mbouhier/HASOR_files/3D printing/stl files/bloceur_alim.stl

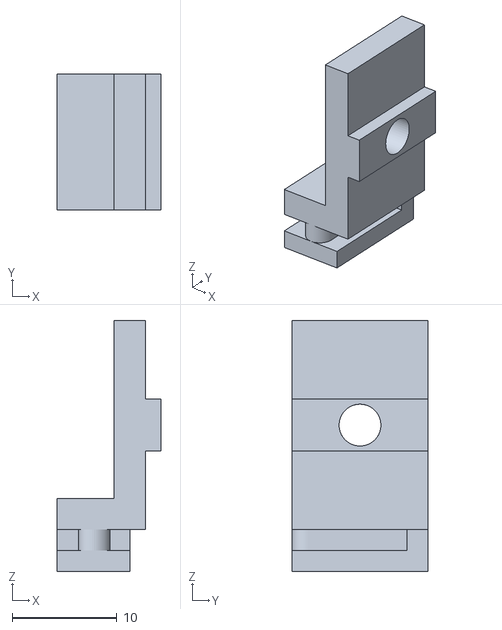
[picture p16: CAD file, 2023-03-02]
3D printing/stl files/bloceur_alim.stl
9.96 x 13.0 x 24.0
