mbouhier/HASOR_files/3D printing/stl files/end_stop_40mm_v3.stl

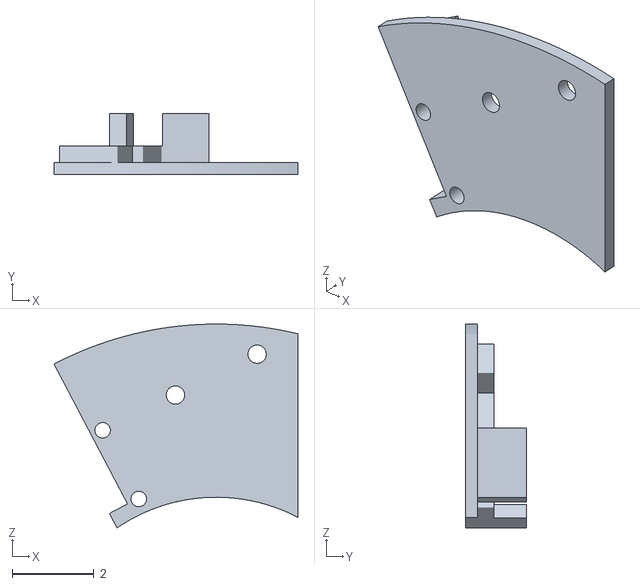
[picture p17: CAD file, 2023-03-02]
3D printing/stl files/end_stop_40mm_v3.stl
5.97 x 1.50 x 4.99
