mbouhier/HASOR_files/3D printing/stl files/support_fourche_principal_simplifie4.stl

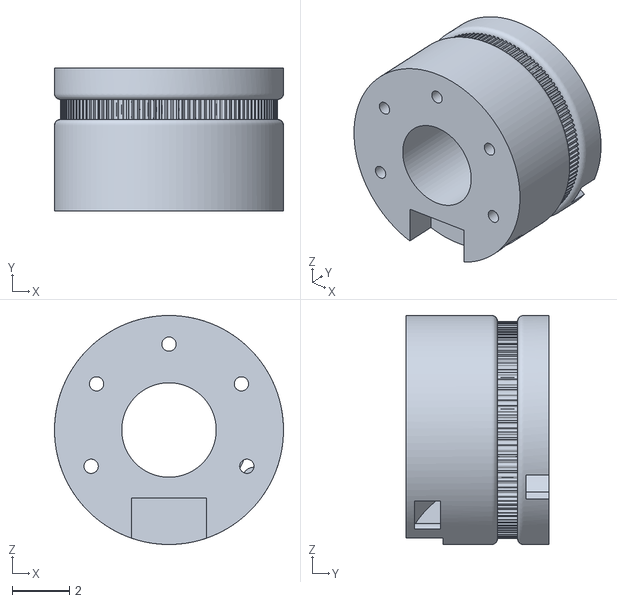
[picture p18: CAD file, 2023-03-02]
3D printing/stl files/support_fourche_principal_simplifie4.stl
8.00 x 5.00 x 8.00
