mbouhier/HASOR_files/3D printing/stl files/espaceur_20mm_v4.stl

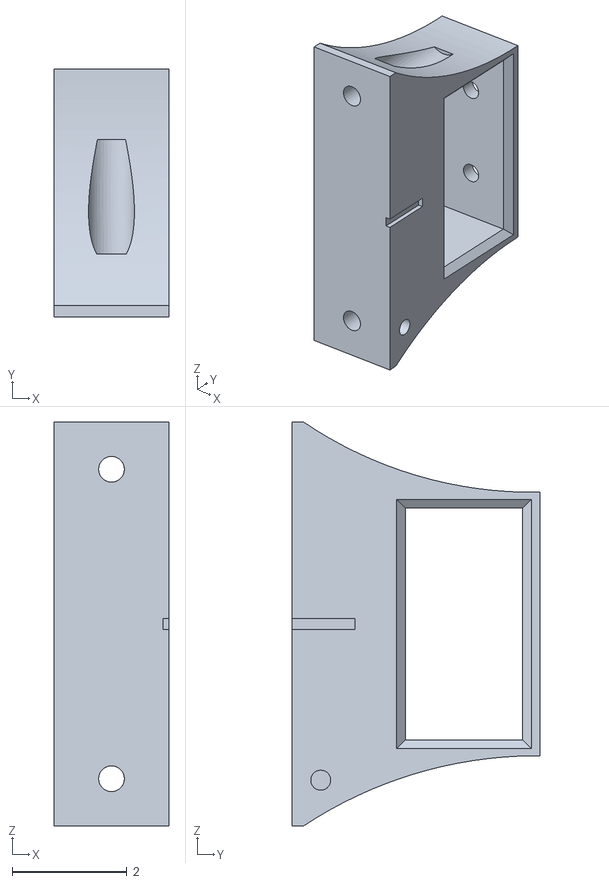
[picture p19: CAD file, 2023-03-02]
3D printing/stl files/espaceur_20mm_v4.stl
2.00 x 4.32 x 7.05
