mbouhier/HASOR_files/3D printing/stl files/support_plateau_v3.stl

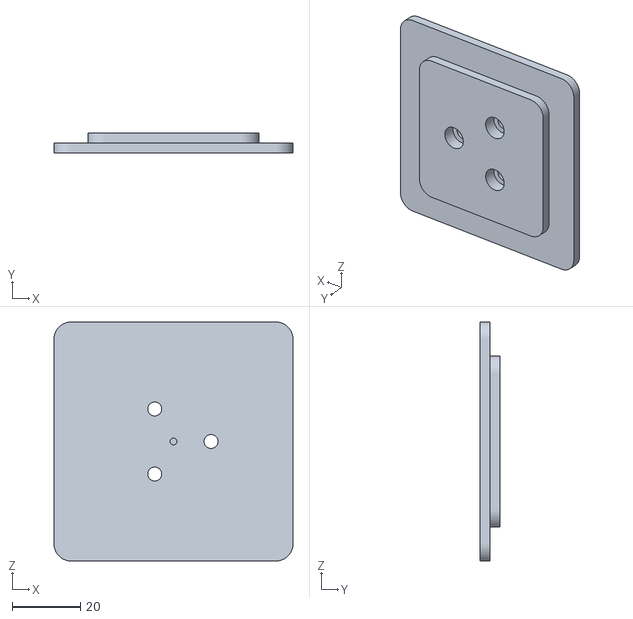
[picture p20: CAD file, 2023-03-02]
3D printing/stl files/support_plateau_v3.stl
70.0 x 6.00 x 70.0
