mbouhier/HASOR_files/3D printing/stl files/support_nema17_40mm.stl

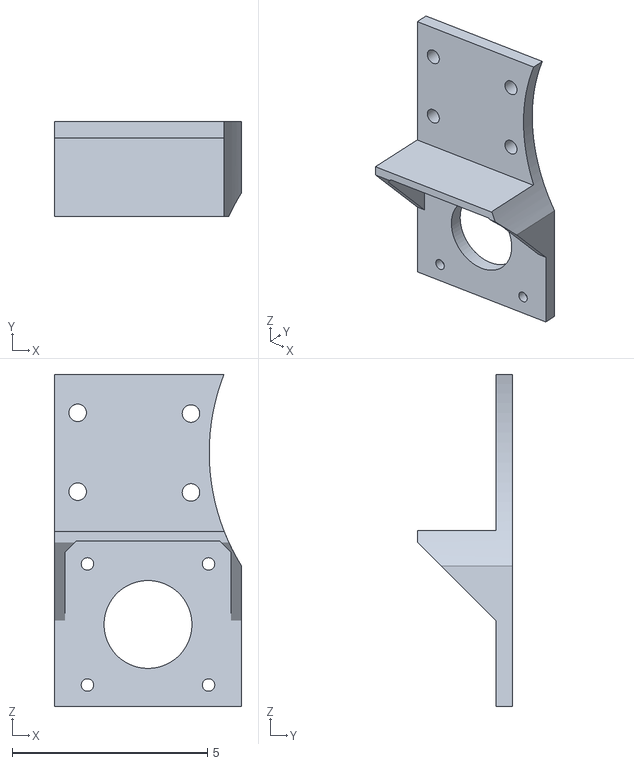
[picture p21: CAD file, 2023-03-02]
3D printing/stl files/support_nema17_40mm.stl
4.80 x 2.42 x 8.50
