mbouhier/HASOR_files/3D printing/stl files/bas_de_fourche_gros_bloc.stl

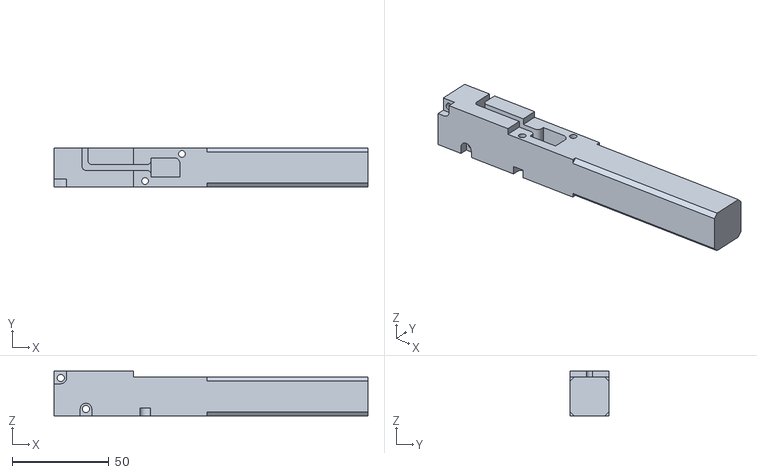
[picture p22: CAD file, 2023-03-02]
3D printing/stl files/bas_de_fourche_gros_bloc.stl
162.0 x 20.0 x 23.0
