mbouhier/HASOR_files/3D printing/stl files/support_fourche_partie_clef.stl

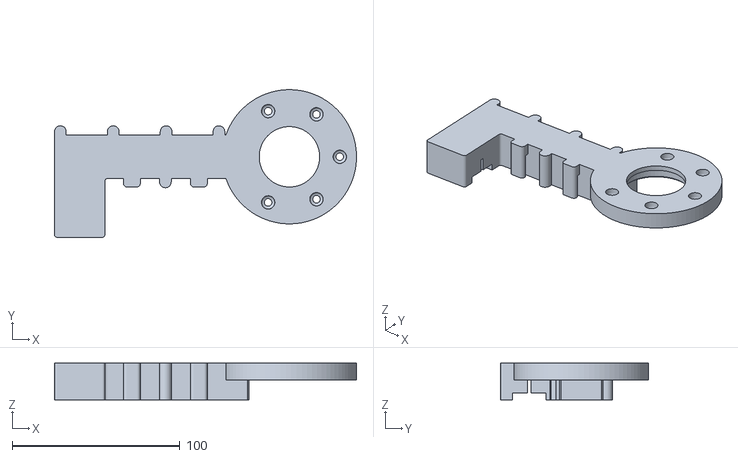
[picture p23: CAD file, 2023-03-02]
3D printing/stl files/support_fourche_partie_clef.stl
180.0 x 88.0 x 22.0
