mbouhier/HASOR_files/3D printing/stl files/guide_nappe_led.stl

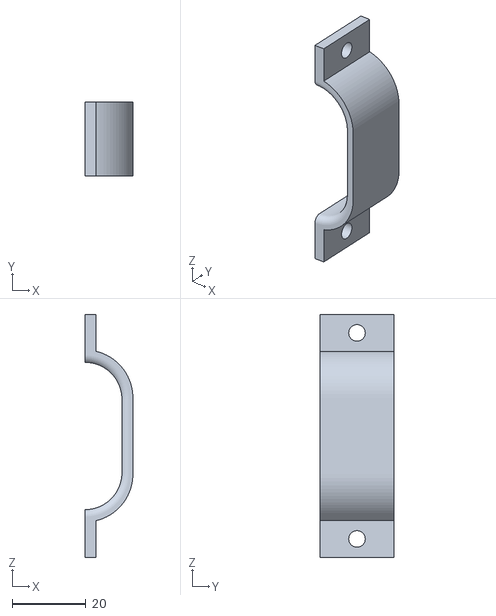
[picture p24: CAD file, 2023-03-02]
3D printing/stl files/guide_nappe_led.stl
13.0 x 20.0 x 66.0
