mbouhier/HASOR_files/3D printing/stl files/fourche_v2_sans_radiateurs.stl

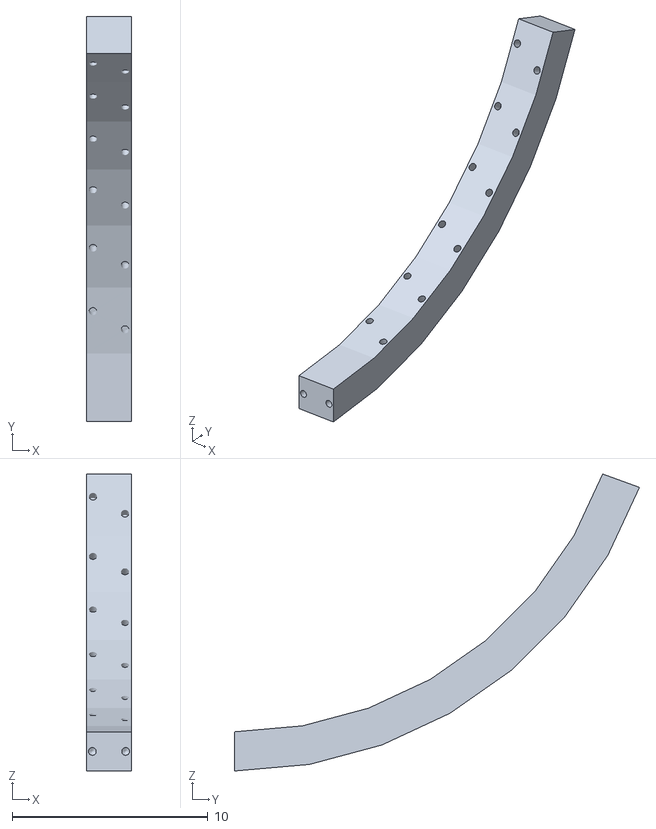
[picture p25: CAD file, 2023-03-02]
3D printing/stl files/fourche_v2_sans_radiateurs.stl
2.30 x 20.7 x 15.2
