mbouhier/HASOR_files/3D printing/stl files/support arduino_v2.stl

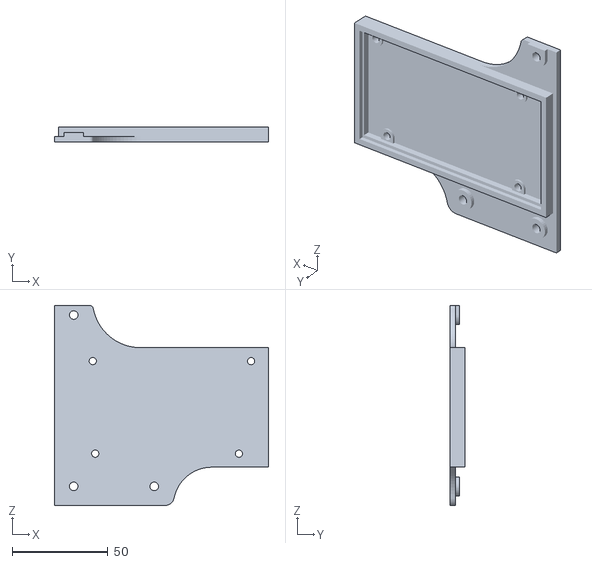
[picture p26: CAD file, 2023-03-02]
3D printing/stl files/support arduino_v2.stl
111.6 x 8.00 x 104.3
