mbouhier/HASOR_files/3D printing/stl files/end_stop_plug_v3.stl

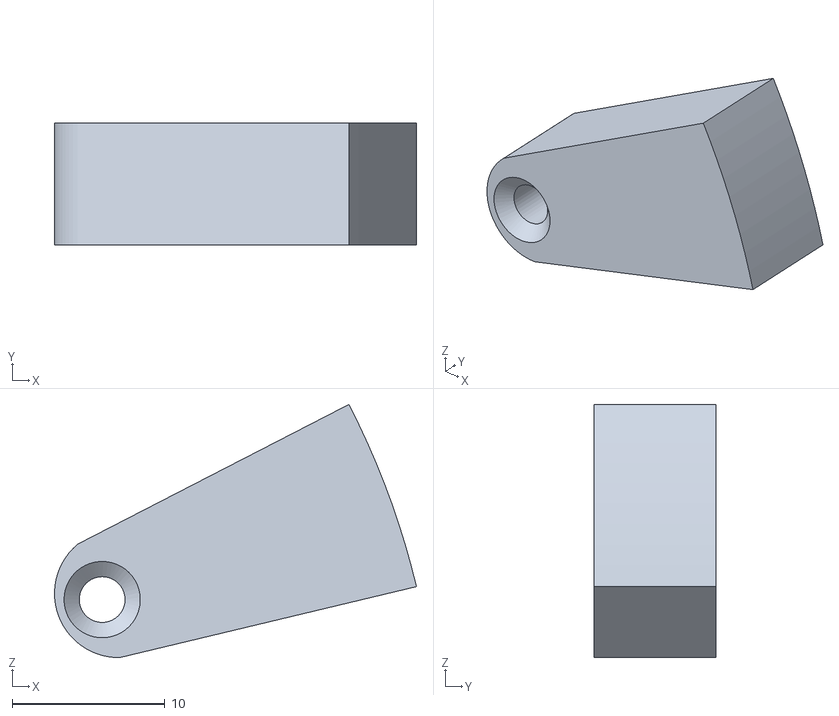
[picture p27: CAD file, 2023-03-02]
3D printing/stl files/end_stop_plug_v3.stl
23.7 x 8.00 x 16.6
